eslam2xm/single-cycle-16-bit-mips-microprocessor/VHDL/ROM/ROM.vhd

----------------------------------------------------------------------------------
-- Company: 
-- Engineer: 
-- 
-- Create Date:    21:17:08 04/08/2019 
-- Design Name: 
-- Module Name:    ROM - Behavioral 
-- Project Name: 
-- Target Devices: 
-- Tool versions: 
-- Description: 
--
-- Dependencies: 
--
-- Revision: 
-- Revision 0.01 - File Created
-- Additional Comments: 
--
----------------------------------------------------------------------------------
library IEEE;
use IEEE.STD_LOGIC_1164.ALL;
use IEEE.std_logic_unsigned.ALL ;
use IEEE.std_logic_arith.ALL ;

-- Uncomment the following library declaration if using
-- arithmetic functions with Signed or Unsigned values
--use IEEE.NUMERIC_STD.ALL;

-- Uncomment the following library declaration if instantiating
-- any Xilinx primitives in this code.
--library UNISIM;
--use UNISIM.VComponents.all;

entity ROM is
	port (
			Address : in std_logic_vector ( 9 downto 0 ) ;
			Data_out : out std_logic_vector ( 15 downto 0 ) );
end ROM;

architecture Behavioral of ROM is

type ram is array ( 0 to(2**12) ) of std_logic_vector ( 15 downto 0 ) ;
constant in_reg : ram := 
("0000000000000001",
"0100000000010000",
"0000000000000110",
"0010000000000000",
"0000110110110001",
"0000001001001001",
"0100110110011111",
"0100110110010100",
"1000110001000000",
"0000110110110001",
"0100110110001001",
"1000110001000000",
"0000100100100001",
"1100000101100011",
"0000110110110001",
"0100110110001001",
"0111110010000000",
"0000001001001001",
"0100001001000001",
"1001010001000001",
"1011000000001101",
"0000010010010001",
"1000110010000000",
"0000110110110001",
"0100110110001000",
"0111110010000000",
"0000001001001001",
"0000010000010111",
"1001010001000001",
"1011000000100000",
"0100100100010100",
"1011000000001101",
"0000010000010111",
"1001010001000001",
"1011000000100101",
"0100100100011001",
"1011000000001101",
"0000010000010111",
"1001010001000001",
"1011000000101010",
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
 others => "1110000000000000"
 );

begin
				Data_out <= in_reg(conv_integer(unsigned(Address))) ;
end Behavioral;
